ykrismmmd/ESP32_HIEYUKARISAN/hardware/ESP32-WROOM-32_開発ボード/719W6JVWl9L._SL1200_.jpg

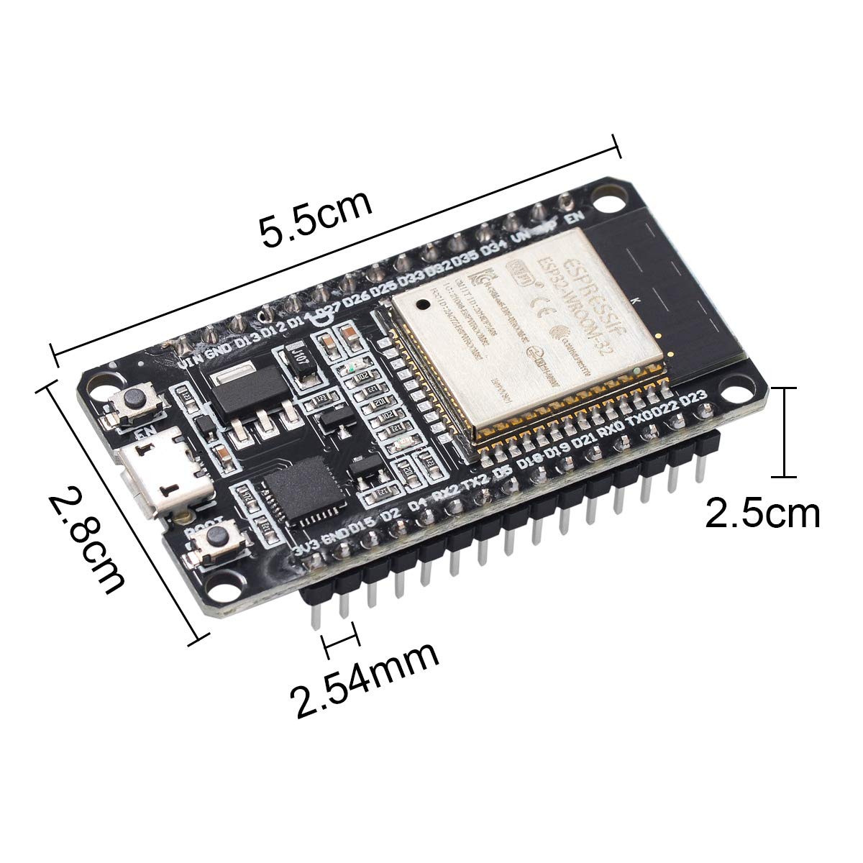
hardware/ESP32-WROOM-32_開発ボード/719W6JVWl9L._SL1200_.jpg
