ykrismmmd/ESP32_HIEYUKARISAN/hardware/HiLetgo_DFPlay_mini/51+Du5sRIiL._SL1100_.jpg

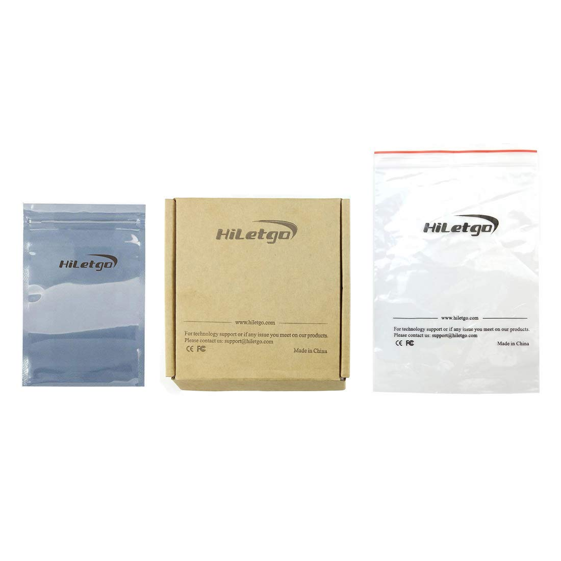
hardware/HiLetgo_DFPlay_mini/51+Du5sRIiL._SL1100_.jpg
