ykrismmmd/ESP32_HIEYUKARISAN/hardware/HiLetgo_DFPlay_mini/51q-+utG1LL._SL1010_.jpg

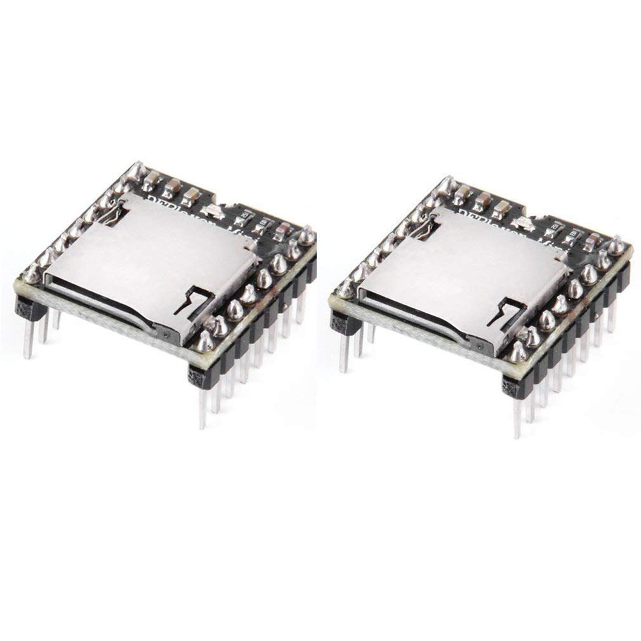
hardware/HiLetgo_DFPlay_mini/51q-+utG1LL._SL1010_.jpg
