ykrismmmd/ESP32_HIEYUKARISAN/hardware/HiLetgo_DFPlay_mini/51Rl7gw1QjL._SL1010_.jpg

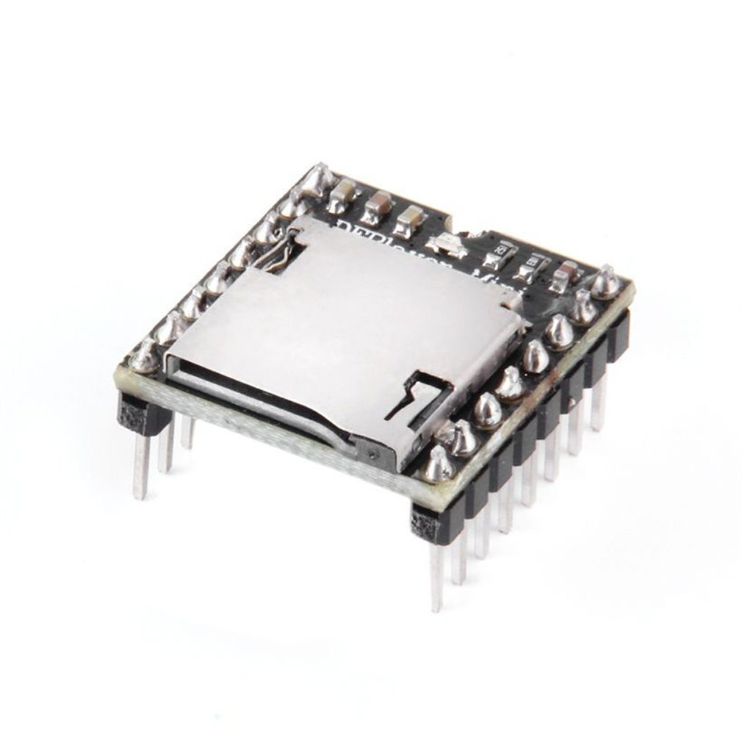
hardware/HiLetgo_DFPlay_mini/51Rl7gw1QjL._SL1010_.jpg
