ykrismmmd/ESP32_HIEYUKARISAN/hardware/HiLetgo_DFPlay_mini/61-qYmQIiwL._SL1010_.jpg

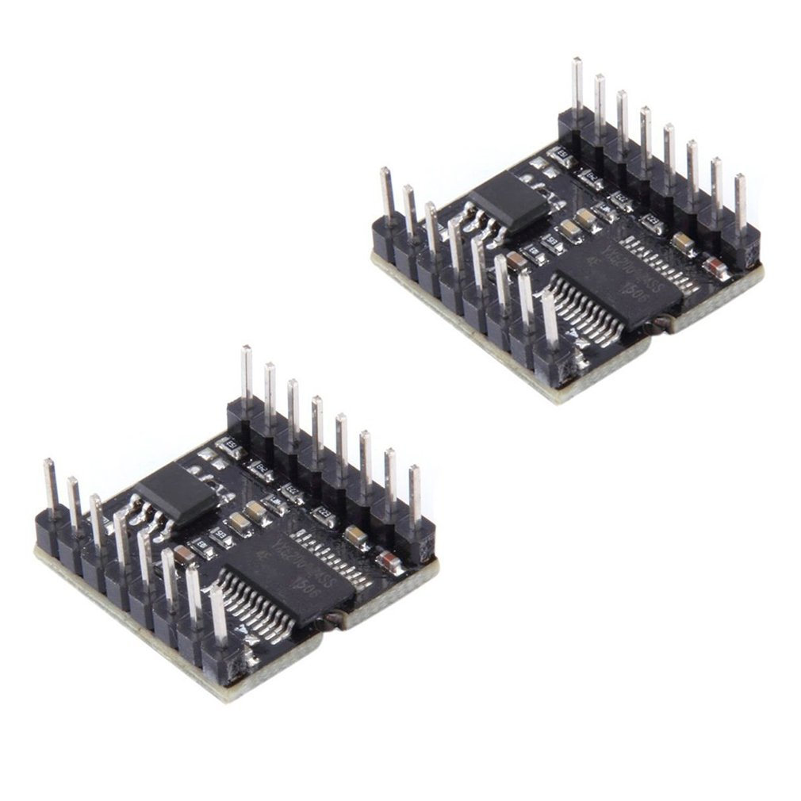
hardware/HiLetgo_DFPlay_mini/61-qYmQIiwL._SL1010_.jpg
