ykrismmmd/ESP32_HIEYUKARISAN/hardware/MicroSD_TFカードメモリシールドモジュール/71d9OC0NN+L._SL1500_.jpg

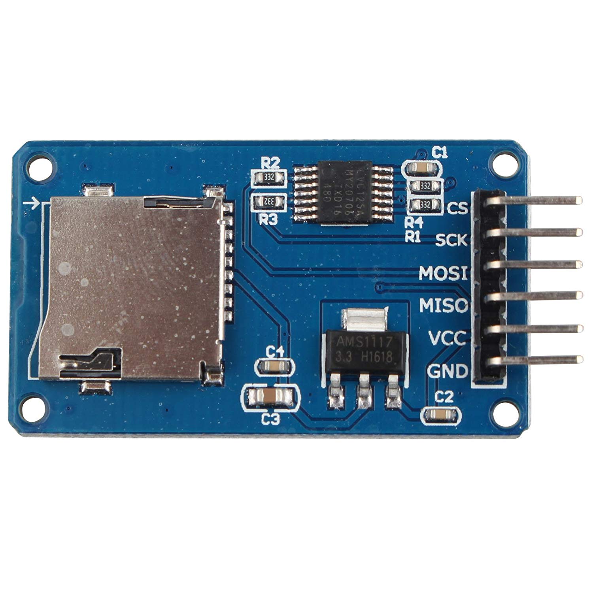
hardware/MicroSD_TFカードメモリシールドモジュール/71d9OC0NN+L._SL1500_.jpg
