ykrismmmd/ESP32_HIEYUKARISAN/hardware/MicroSD_TFカードメモリシールドモジュール/71QkUp7-KtL._SL1500_.jpg

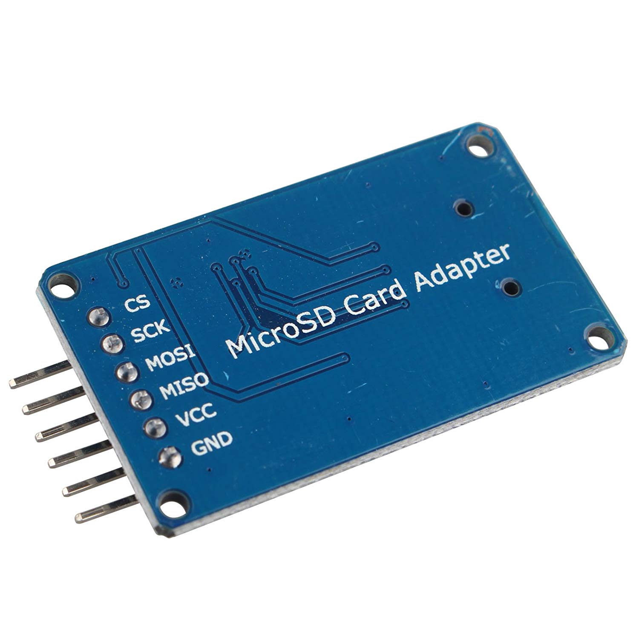
hardware/MicroSD_TFカードメモリシールドモジュール/71QkUp7-KtL._SL1500_.jpg
