ykrismmmd/ESP32_HIEYUKARISAN/hardware/MicroSD_TFカードメモリシールドモジュール/81vch8VJsGL._SL1500_.jpg

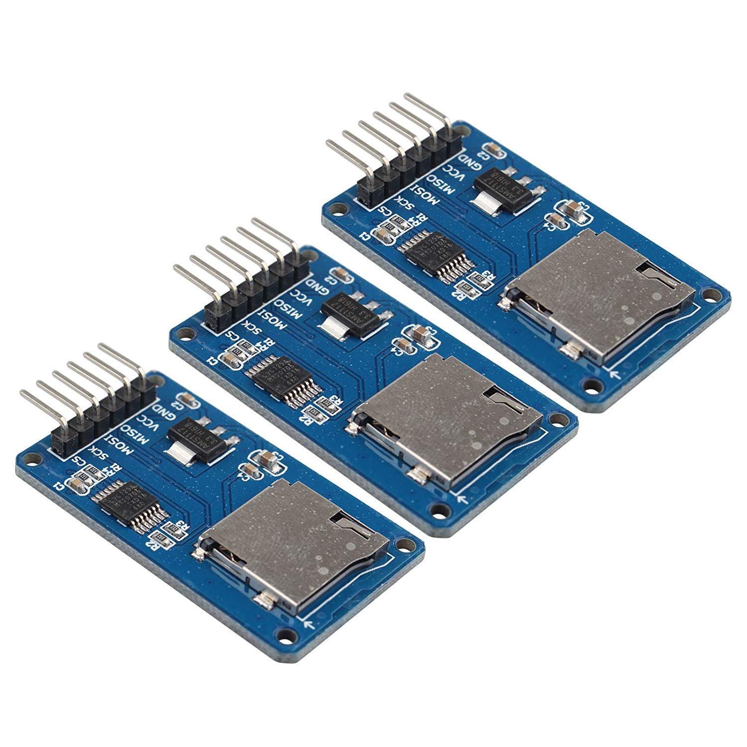
hardware/MicroSD_TFカードメモリシールドモジュール/81vch8VJsGL._SL1500_.jpg
