ykrismmmd/ESP32_HIEYUKARISAN/hardware/MicroSD_TFカードメモリシールドモジュール/715J1rsaGlL._SL1500_.jpg

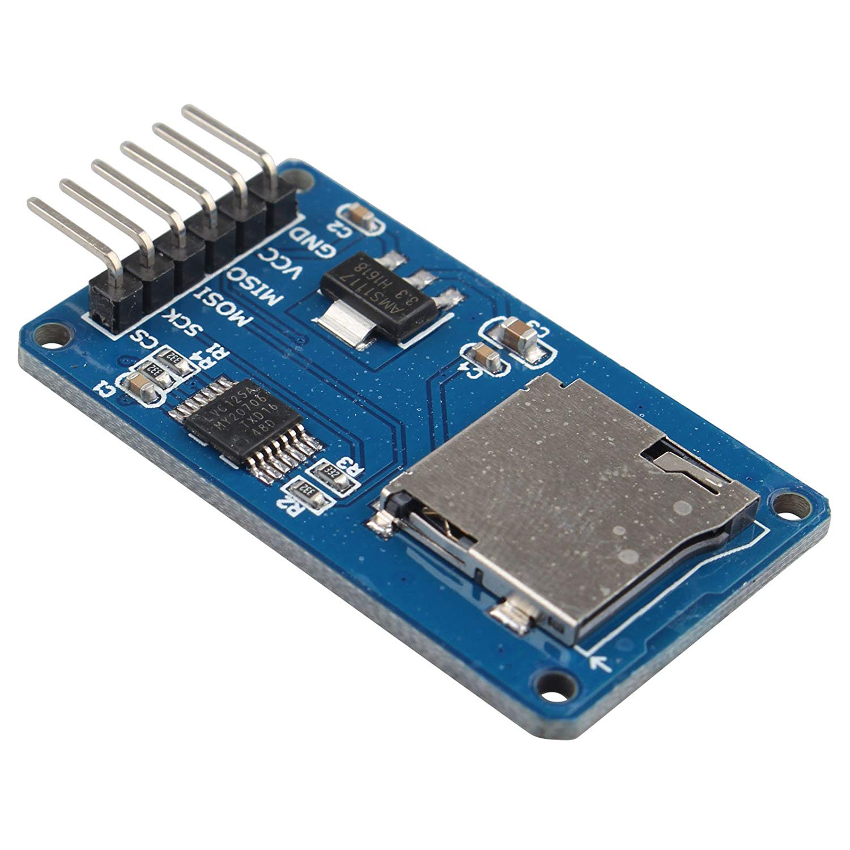
hardware/MicroSD_TFカードメモリシールドモジュール/715J1rsaGlL._SL1500_.jpg
