ykrismmmd/ESP32_HIEYUKARISAN/hardware/ブレッドボード/202203110910_ブレッドボード.png

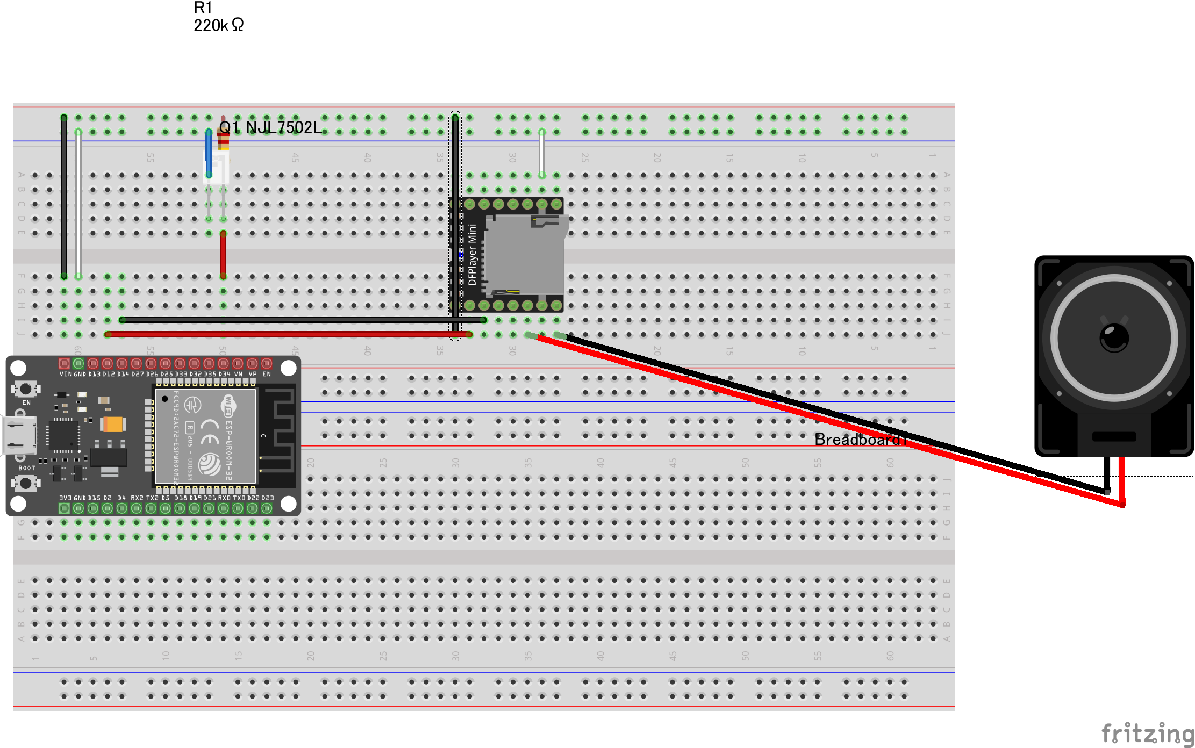
hardware/ブレッドボード/202203110910_ブレッドボード.png
